VerabelGonzales/vera_multi_robot_platform/images_robot_readme/Partes_Robot.png

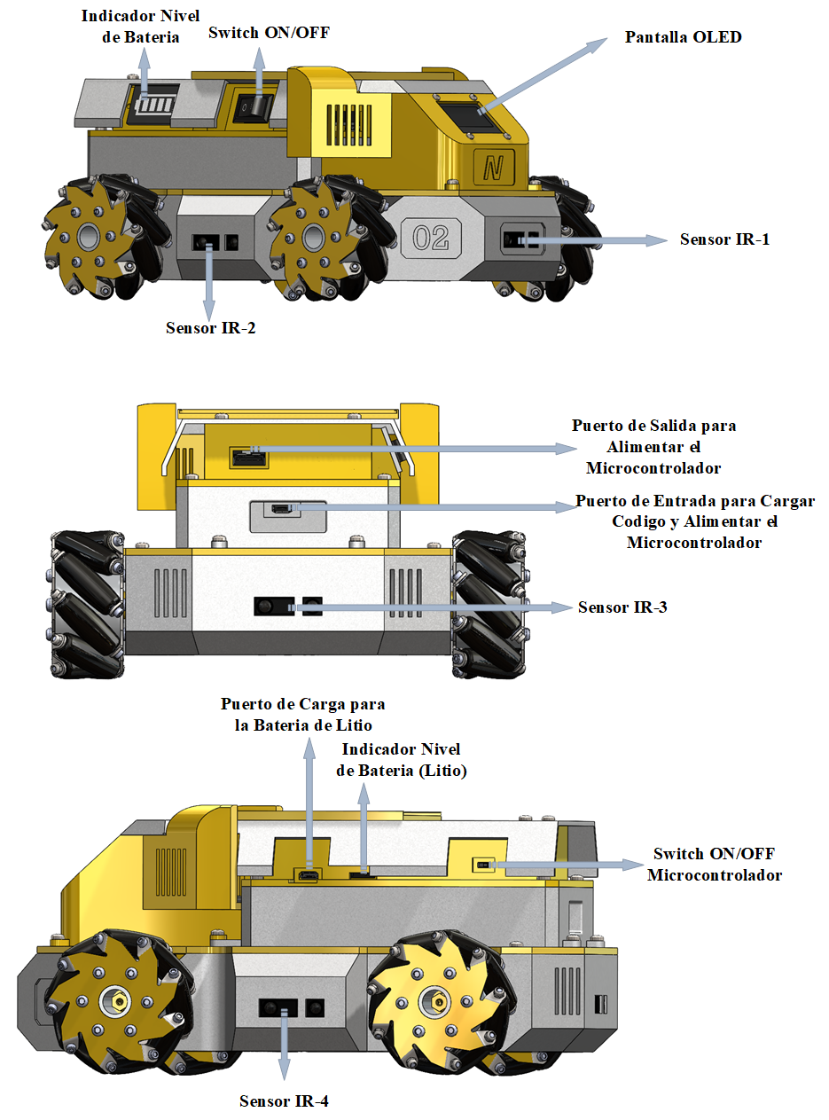
images_robot_readme/Partes_Robot.png
